stefanielinear/ai4ee-pcb/ECG12_Portable/output/3d/pcb_3d_back.png

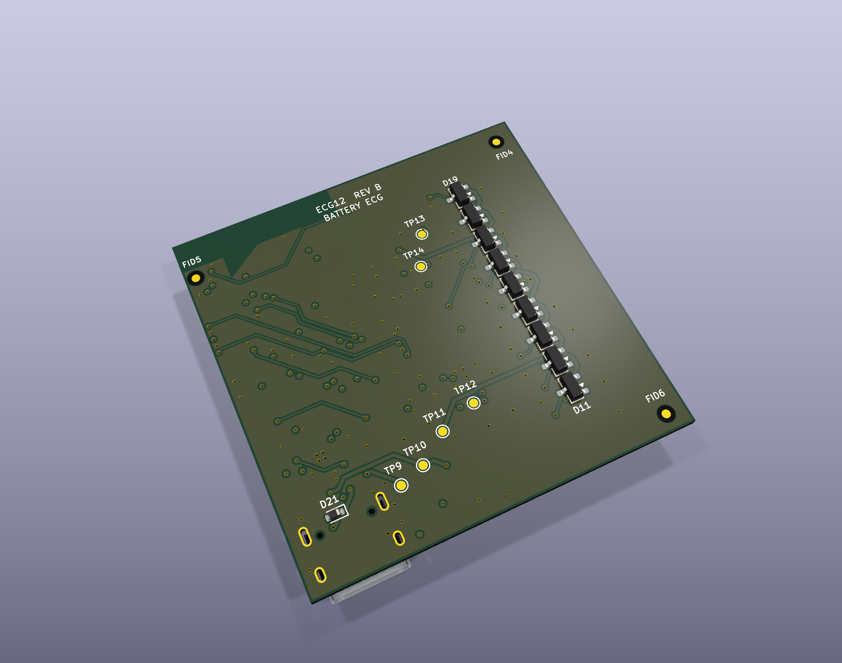
ECG12_Portable/output/3d/pcb_3d_back.png
