stefanielinear/ai4ee-pcb/ECG12_Portable/output/3d/pcb_3d_front.png

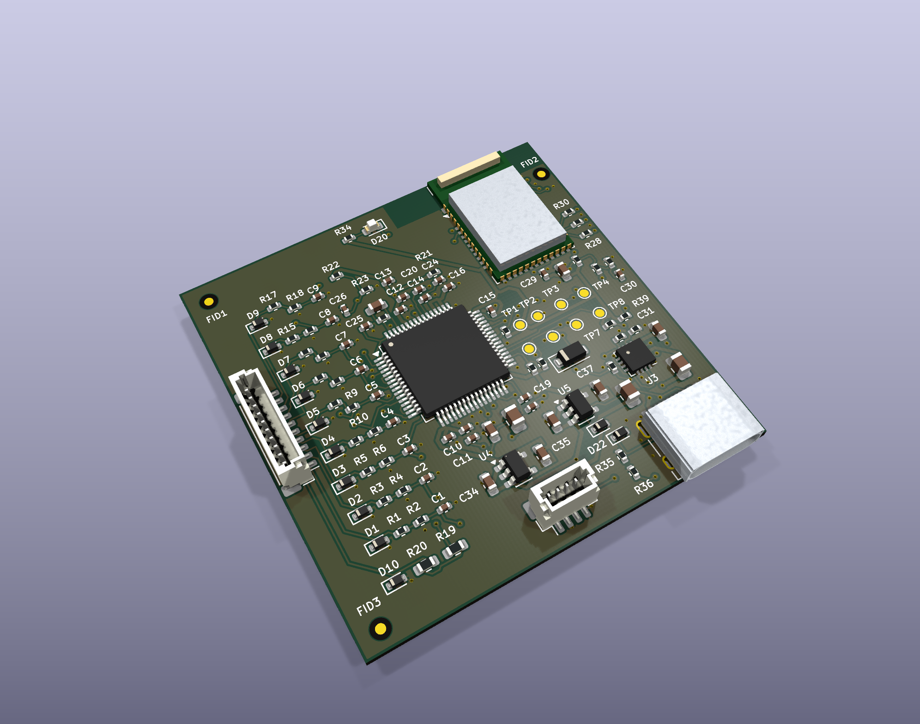
ECG12_Portable/output/3d/pcb_3d_front.png
