stefanielinear/ai4ee-pcb/ECG12_Portable/output/layers/pdf/11_F_Fab.pdf

BAT+ G NTC G | USB CHARGE
C32C32 R26R26 | R39R39 C15C15 C21C21 R12R12 | R33R33 C25C25 | R41R41 R5R5 R15R15 | TP5 TP5
C1C1 | U2 U2

D8 D8

D5 D5

J2J2 R16R16 | R21R21 C10C10 C7C7 | C27 C27 | D22 D22

D6 D6

R3R3 D1 D1

U3U R10R10 | TP1 TP1

R31R31

## FID3 FIDUCIAL

FID3 | R40R40 | R29R29 C11C11 | C35C35 R7R7 | R28R28 FID1 FIDUCIAL
FID1 | TP6 TP6

TP3 TP3

R14R14 R4R4 R6R6 | C4C4 | C33C33 R9R9 | J3J R24R24 C26C26 | C31C31 FID2 FIDUCIAL
FID2 R22R22 | C12C12 C3C3 D10 D10

C29C29 D4 D4

C8C8 | TP8 TP8
R1R1 | C22C22 R11R11 | C18C18 C6C6 | TP2 TP2
C23C23 | C19C19 J1J1
R23R23 R18R18 | C36C36 R27R27 C16C16 | U5U5
R35R35 | R32R32 D3 D3
R36R36 C9C9 | U1U1 | D23 D23 C34C34 R13R13 | D20 D20 C5C5 | R38R38 R37R37 | C28C28 D7 D7
R20 R20 | C14C14 C13C13 | R25R25 R8R8 | TP4 TP4
U4U4 C20C20 R34R34 R17R17 | C17C17 C2C2 R2R2 | C30C30 R19 R19 | D24 D24

R30R30 D2 D2

D9 D9

C24C24 | TP7 TP7

C37C37
