stefanielinear/ai4ee-pcb/ECG12_Portable/output/3d/module_dimensions.png

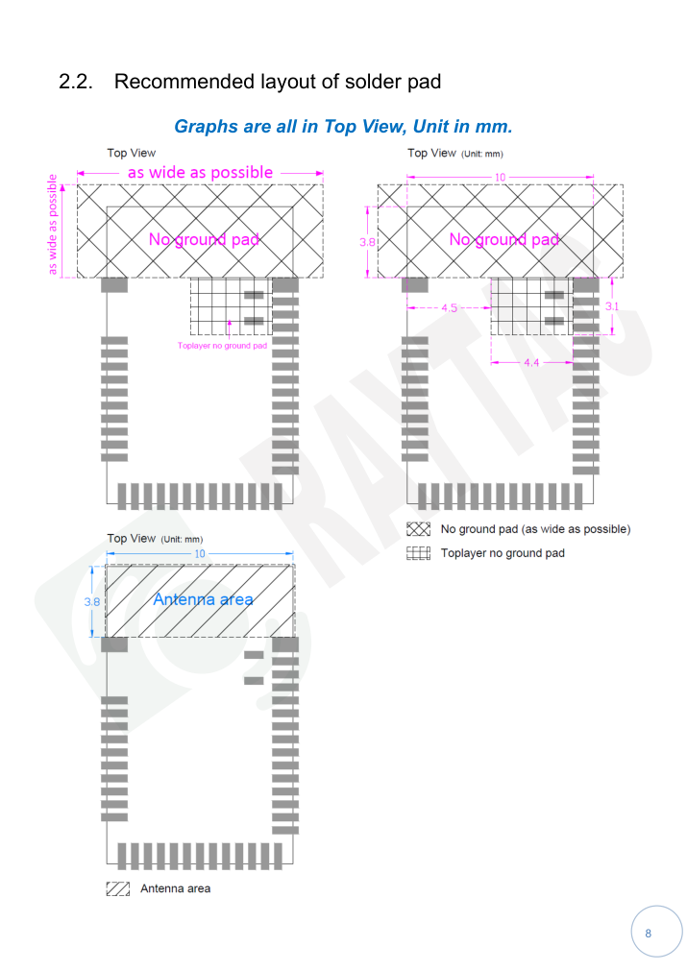
ECG12_Portable/output/3d/module_dimensions.png
