stefanielinear/ai4ee-pcb/ECG12_Portable/output/layers/01_F_Cu.png

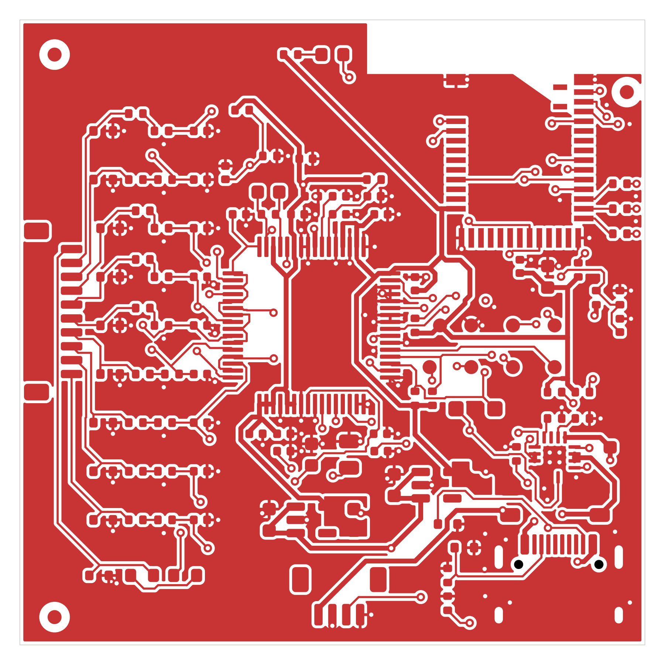
ECG12_Portable/output/layers/01_F_Cu.png
