stefanielinear/ai4ee-pcb/ECG12_Portable/output/layers/02_In1_Cu.png

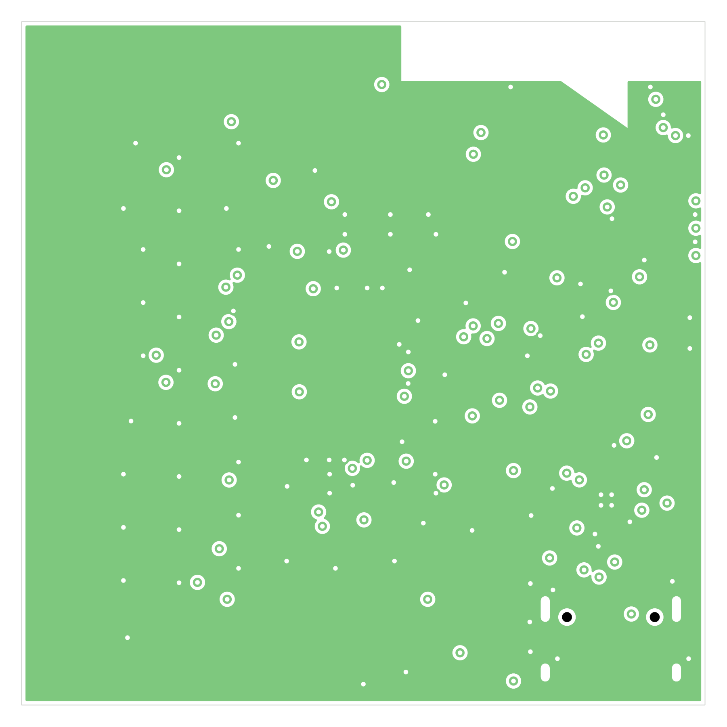
ECG12_Portable/output/layers/02_In1_Cu.png
