stefanielinear/ai4ee-pcb/ECG12_Portable/output/layers/03_In2_Cu.png

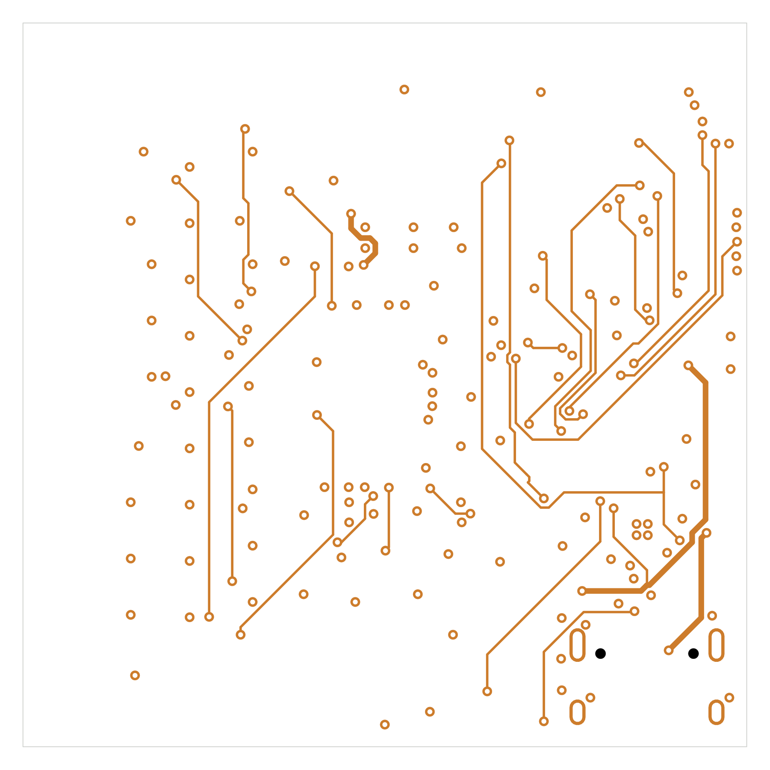
ECG12_Portable/output/layers/03_In2_Cu.png
