stefanielinear/ai4ee-pcb/ECG12_Portable/output/layers/04_B_Cu.png

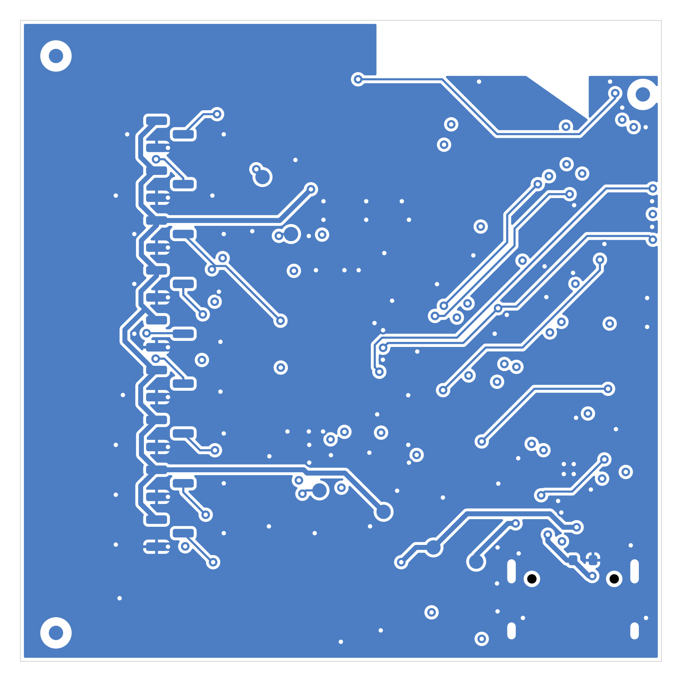
ECG12_Portable/output/layers/04_B_Cu.png
