stefanielinear/ai4ee-pcb/ECG12_Portable/output/layers/05_F_Mask.png

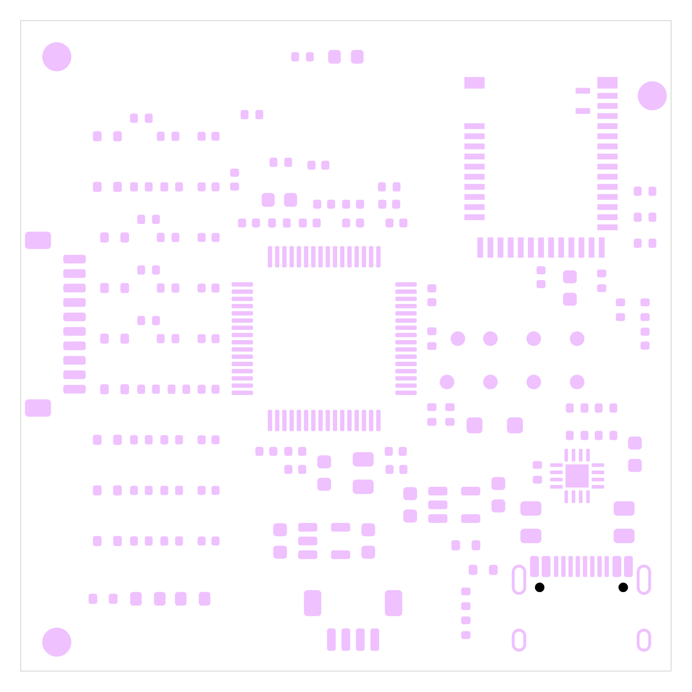
ECG12_Portable/output/layers/05_F_Mask.png
