stefanielinear/ai4ee-pcb/ECG12_Portable/output/layers/06_B_Mask.png

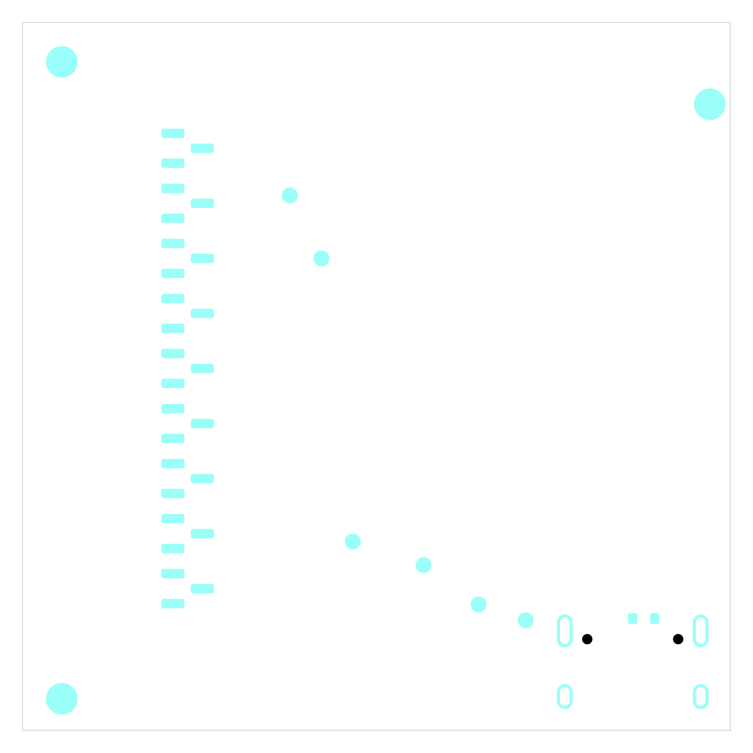
ECG12_Portable/output/layers/06_B_Mask.png
