stefanielinear/ai4ee-pcb/ECG12_Portable/output/layers/07_F_Paste.png

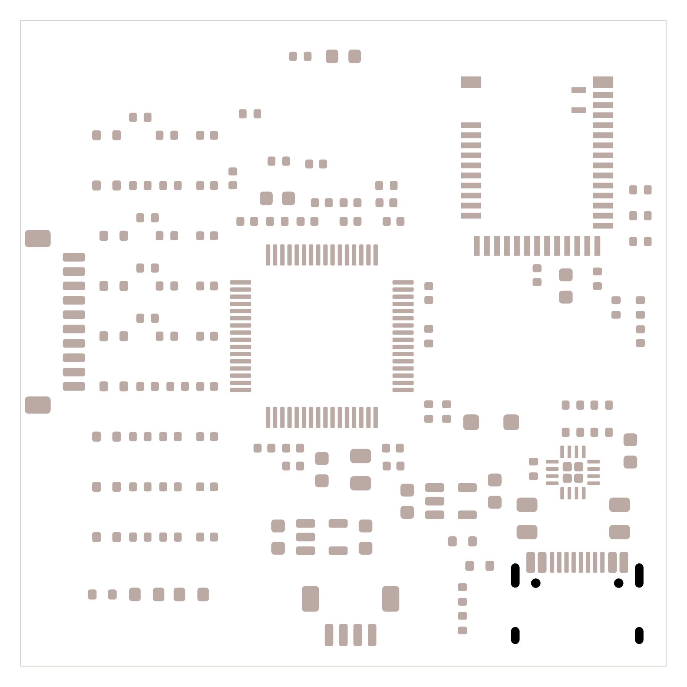
ECG12_Portable/output/layers/07_F_Paste.png
