stefanielinear/ai4ee-pcb/ECG12_Portable/output/layers/08_B_Paste.png

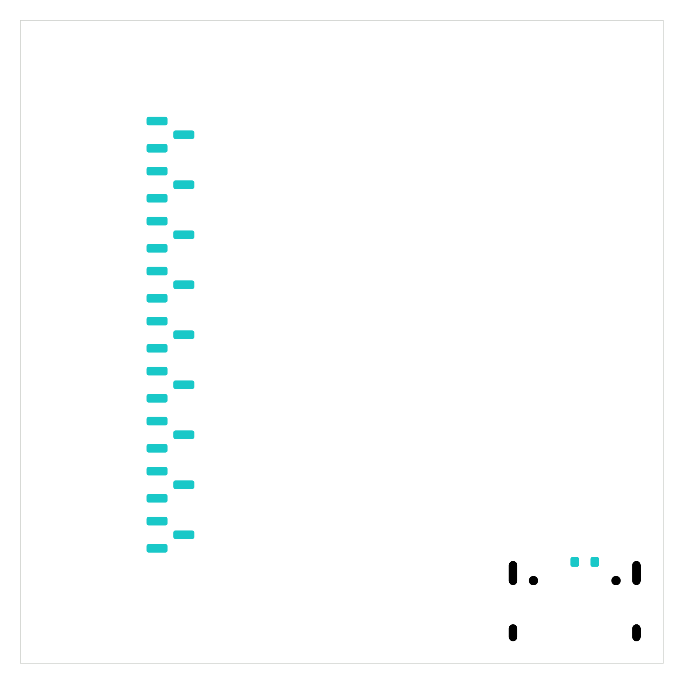
ECG12_Portable/output/layers/08_B_Paste.png
