stefanielinear/ai4ee-pcb/ECG12_Portable/output/layers/09_F_Silkscreen.png

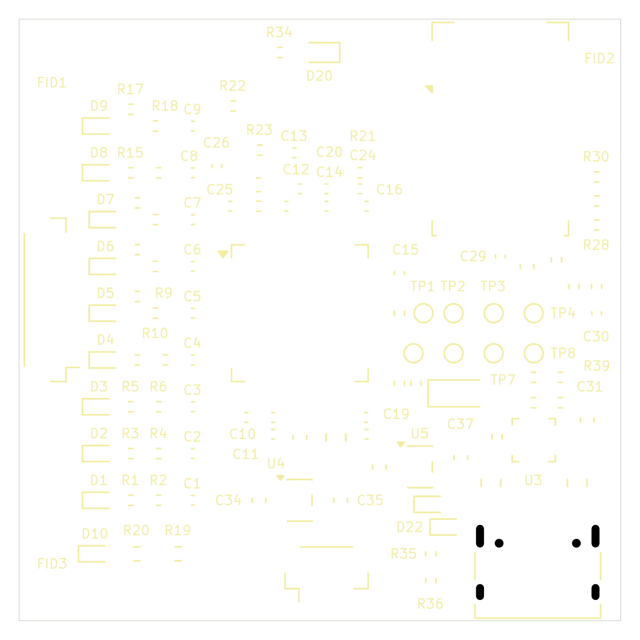
ECG12_Portable/output/layers/09_F_Silkscreen.png
