stefanielinear/ai4ee-pcb/ECG12_Portable/output/layers/10_B_Silkscreen.png

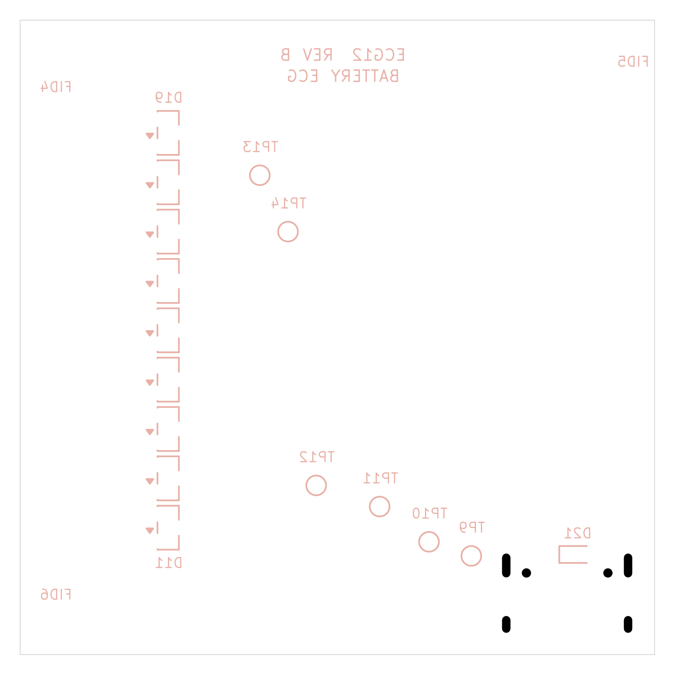
ECG12_Portable/output/layers/10_B_Silkscreen.png
