stefanielinear/ai4ee-pcb/ECG12_Portable/output/layers/11_F_Fab.png

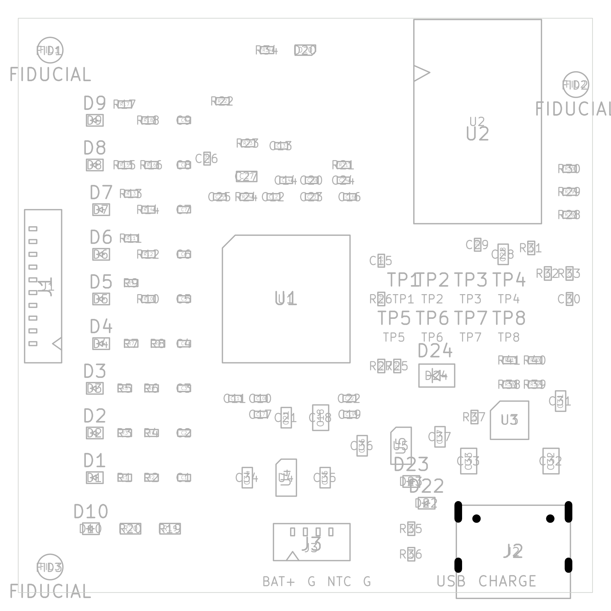
ECG12_Portable/output/layers/11_F_Fab.png
