stefanielinear/ai4ee-pcb/ECG12_Portable/output/layers/12_B_Fab.png

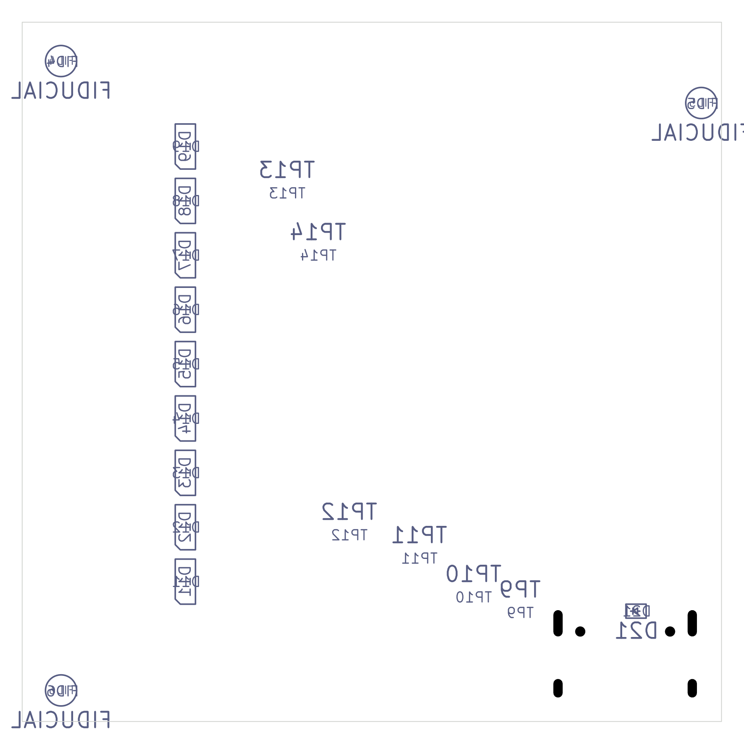
ECG12_Portable/output/layers/12_B_Fab.png
