stefanielinear/ai4ee-pcb/ECG12_Portable/output/layers/13_F_Courtyard.png

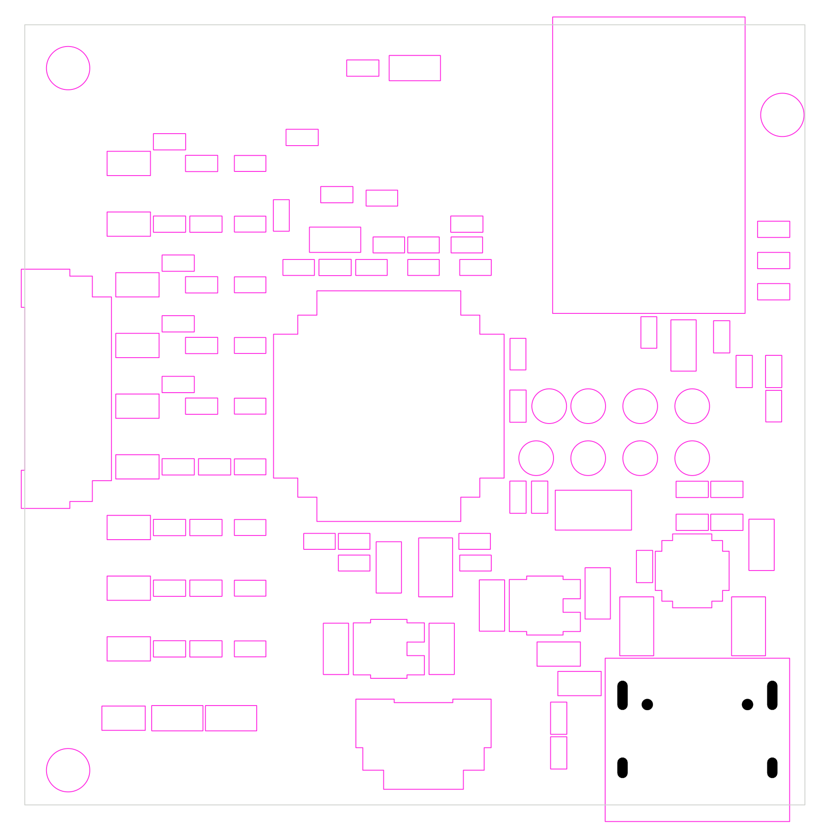
ECG12_Portable/output/layers/13_F_Courtyard.png
