stefanielinear/ai4ee-pcb/ECG12_Portable/output/layers/15_Edge_Cuts.png

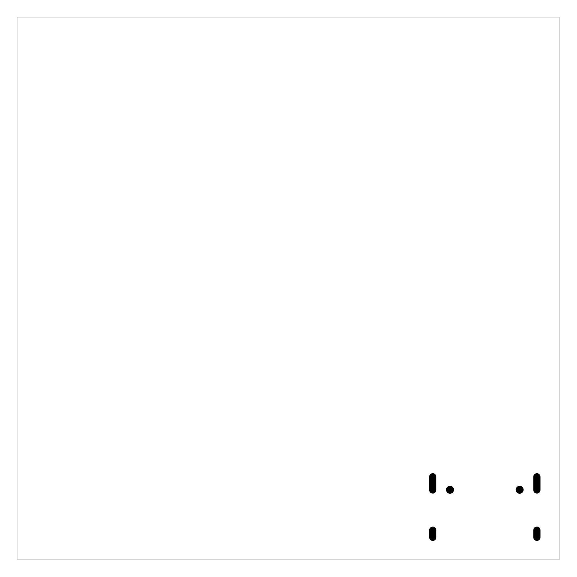
ECG12_Portable/output/layers/15_Edge_Cuts.png
