stefanielinear/ai4ee-pcb/ECG12_Portable/output/layers/copper_layers_overview.png

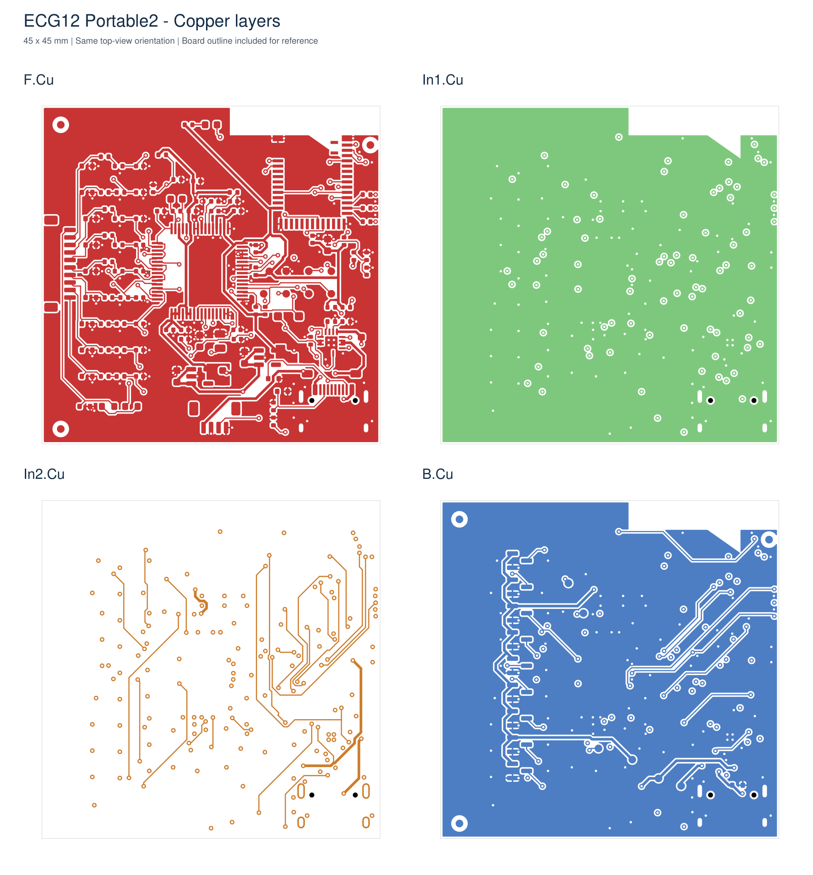
ECG12_Portable/output/layers/copper_layers_overview.png
