stefanielinear/ai4ee-pcb/ECG12_Portable/output/schematic_images/01_System.png

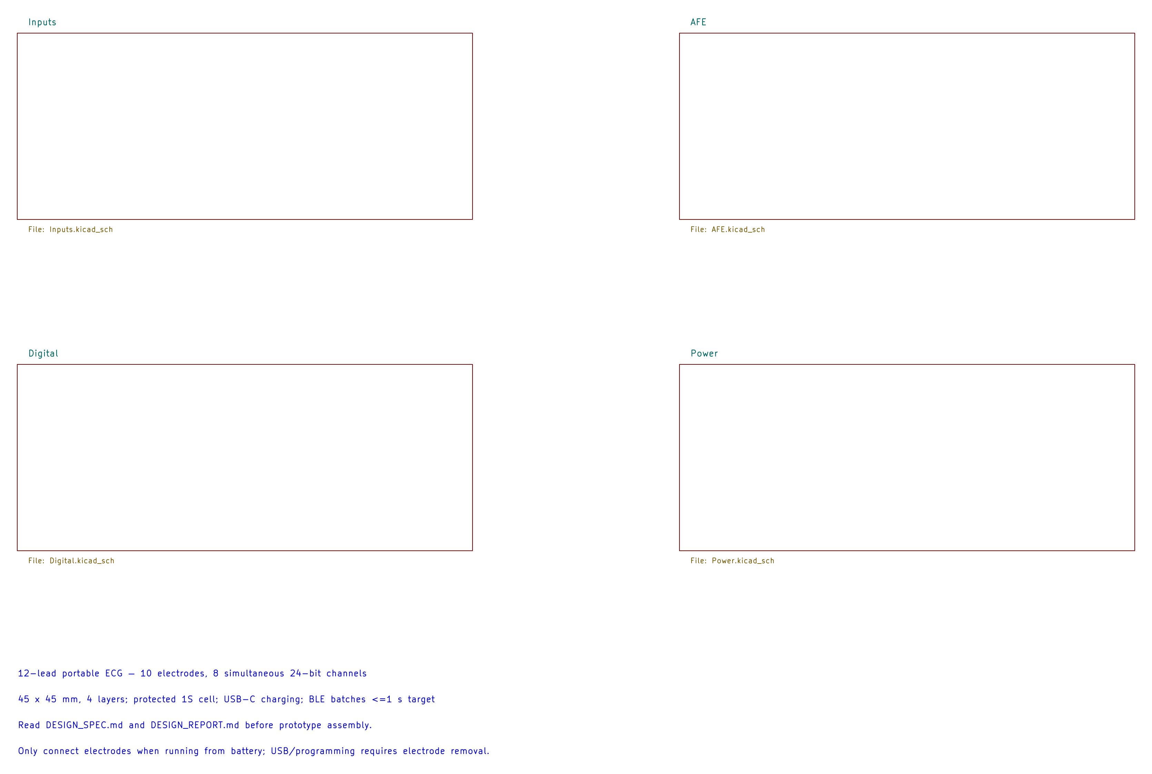
ECG12_Portable/output/schematic_images/01_System.png
