stefanielinear/ai4ee-pcb/ECG12_Portable/output/schematic_images/02_Inputs.png

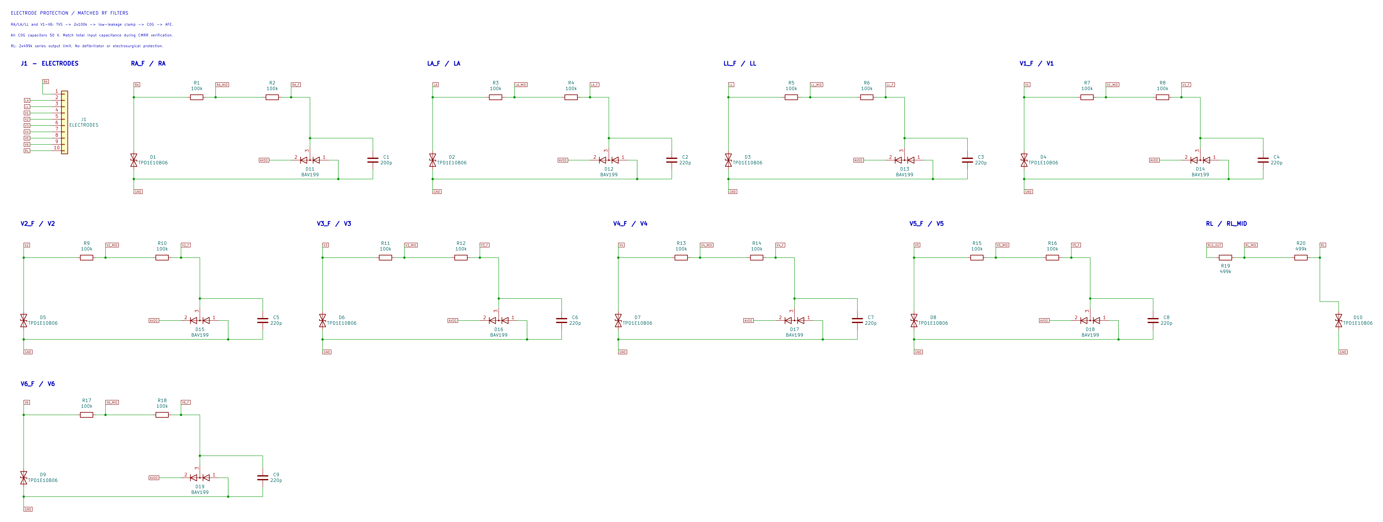
ECG12_Portable/output/schematic_images/02_Inputs.png
