stefanielinear/ai4ee-pcb/ECG12_Portable/output/schematic_images/03_AFE.png

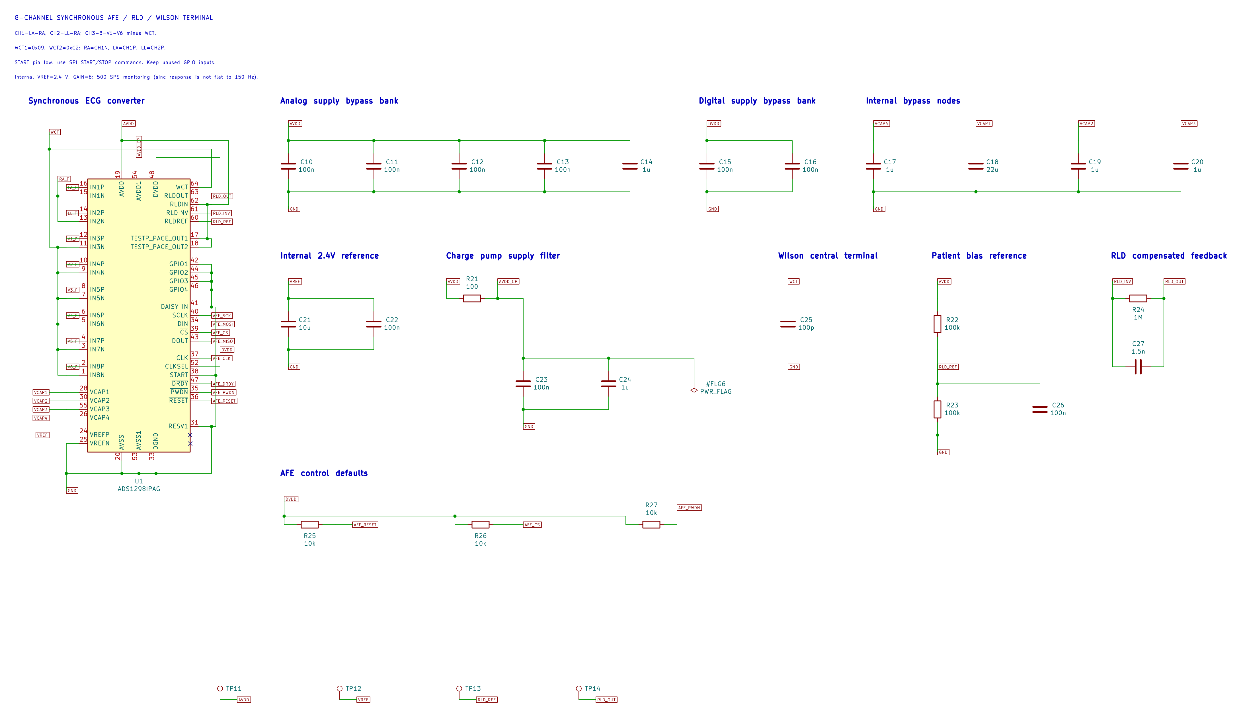
ECG12_Portable/output/schematic_images/03_AFE.png
