stefanielinear/ai4ee-pcb/ECG12_Portable/output/schematic_images/04_Digital.png

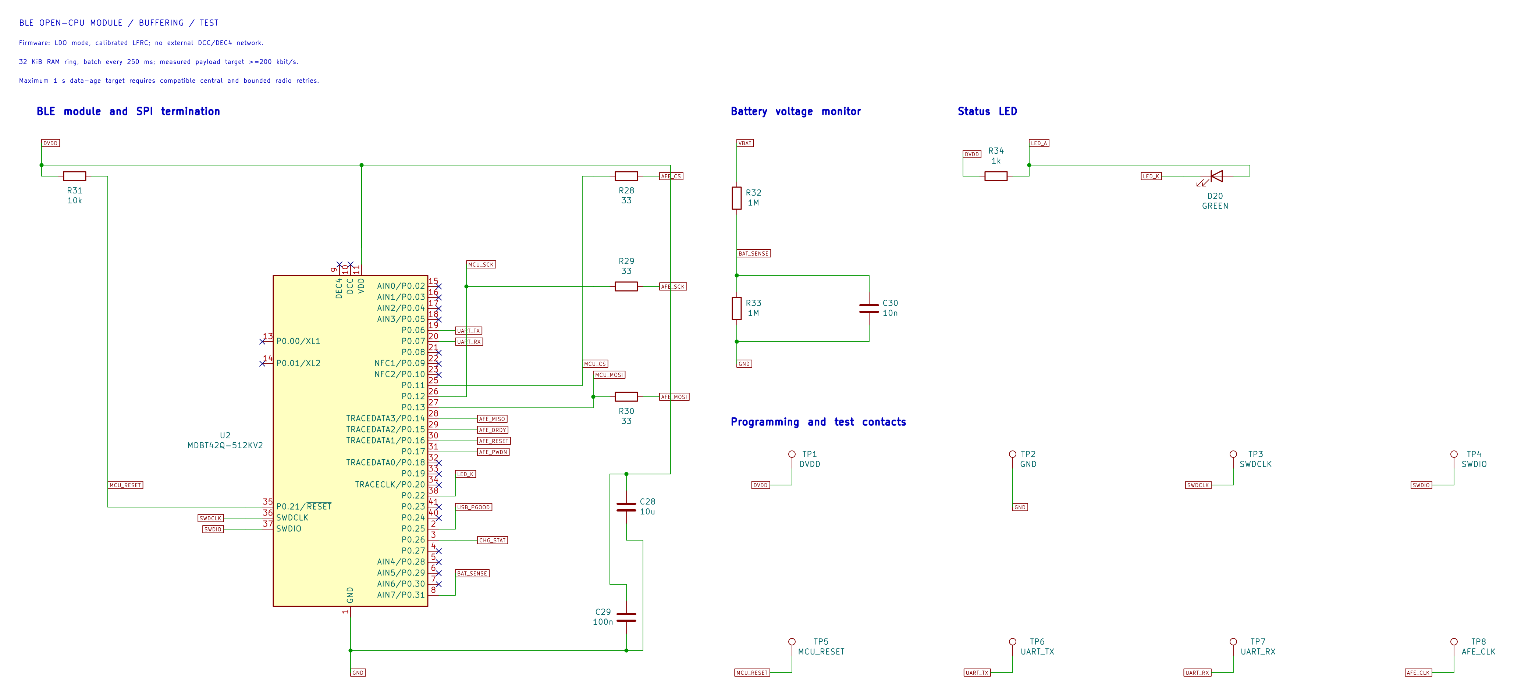
ECG12_Portable/output/schematic_images/04_Digital.png
