stefanielinear/ai4ee-pcb/ECG12_Portable/output/schematic_images/full_pages/01_System.png

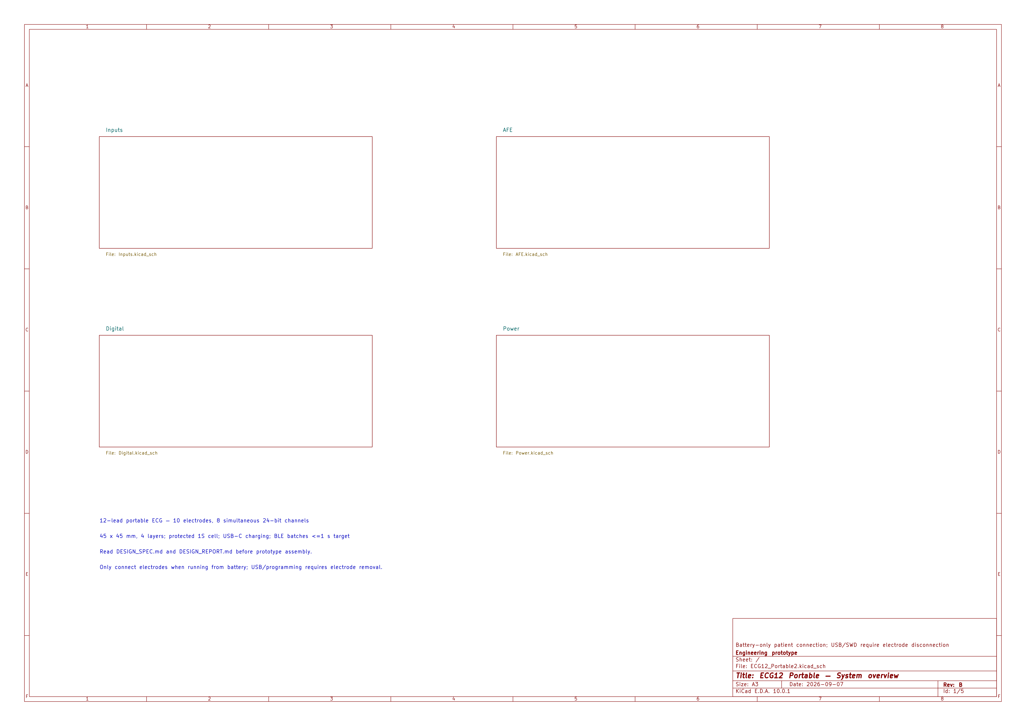
ECG12_Portable/output/schematic_images/full_pages/01_System.png
