stefanielinear/ai4ee-pcb/ECG12_Portable/output/schematic_images/full_pages/04_Digital.png

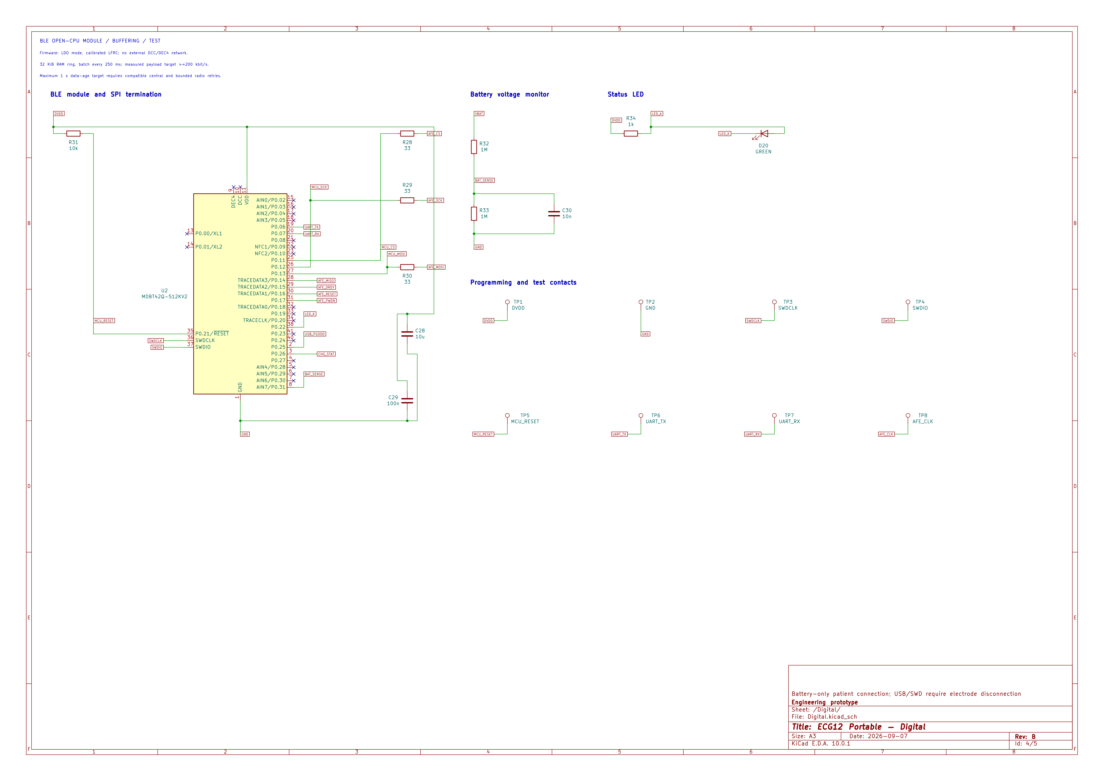
ECG12_Portable/output/schematic_images/full_pages/04_Digital.png
