stefanielinear/ai4ee-pcb/ECG12_Portable/output/schematic_images/full_pages/05_Power.png

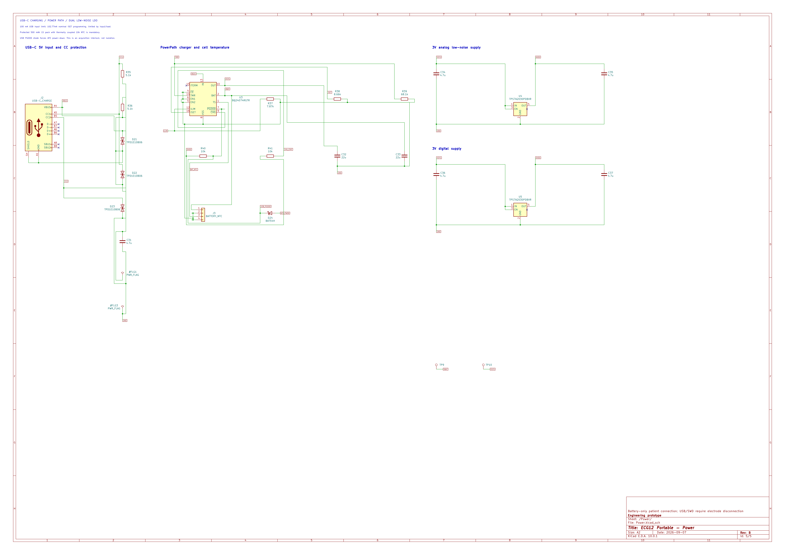
ECG12_Portable/output/schematic_images/full_pages/05_Power.png
