stefanielinear/ai4ee-pcb/ECG12_Portable/output/schematic_images/overview.png

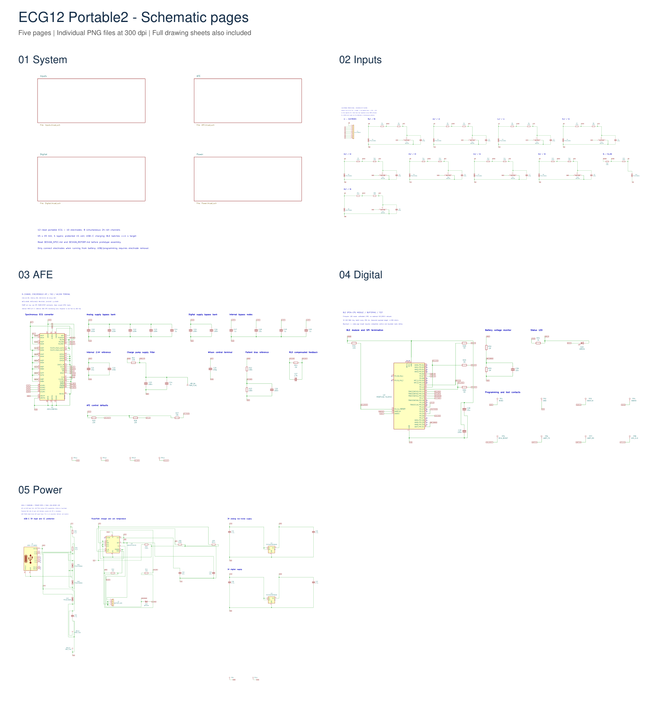
ECG12_Portable/output/schematic_images/overview.png
