stefanielinear/ai4ee-pcb/ECG12_Portable/production/drawings/ground_plane.pdf

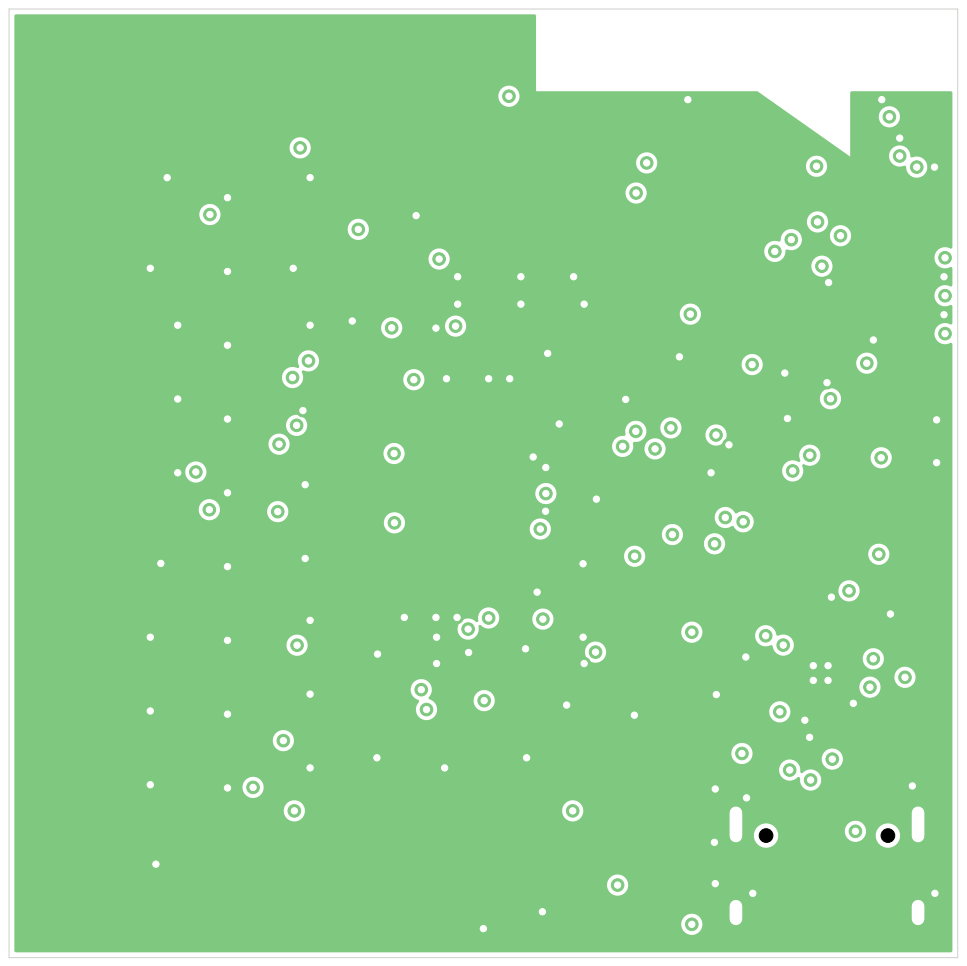
[picture p69: page 1]
