stefanielinear/ai4ee-pcb/ECG12_Portable/output/layers/pdf/01_F_Cu.pdf

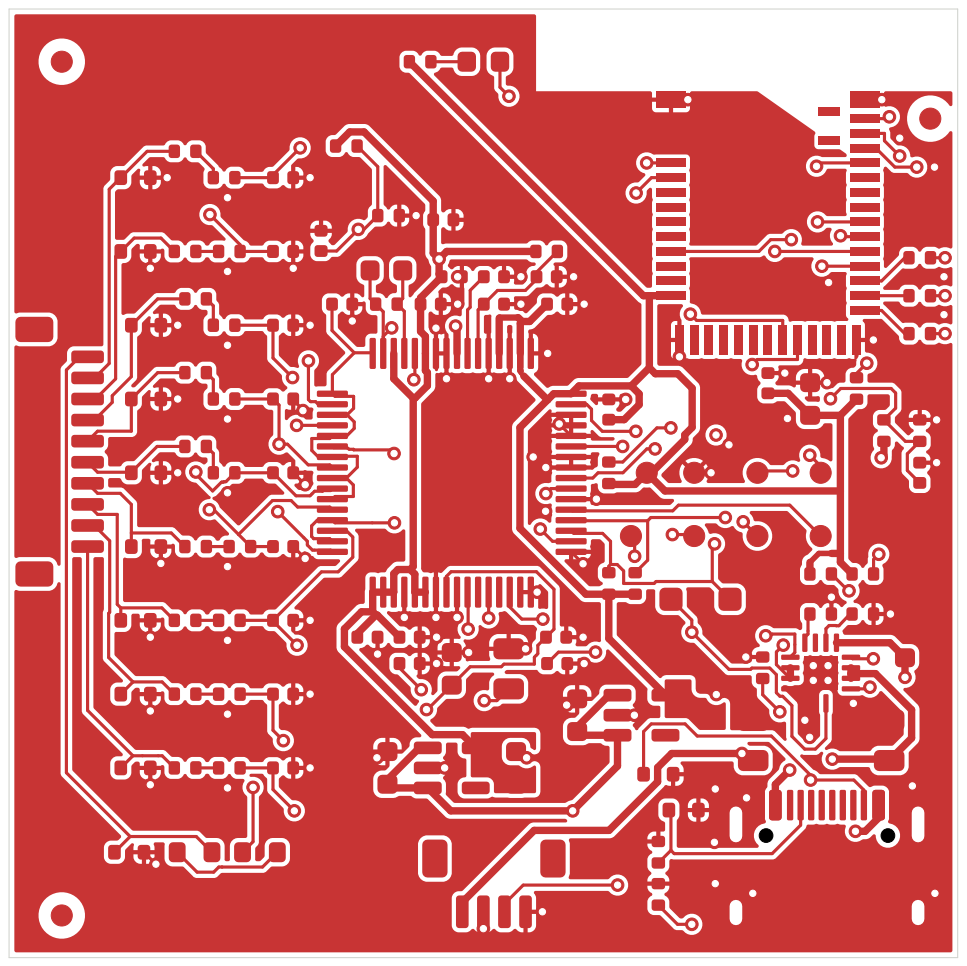
[picture p70: page 1]
