stefanielinear/ai4ee-pcb/ECG12_Portable/output/layers/pdf/03_In2_Cu.pdf

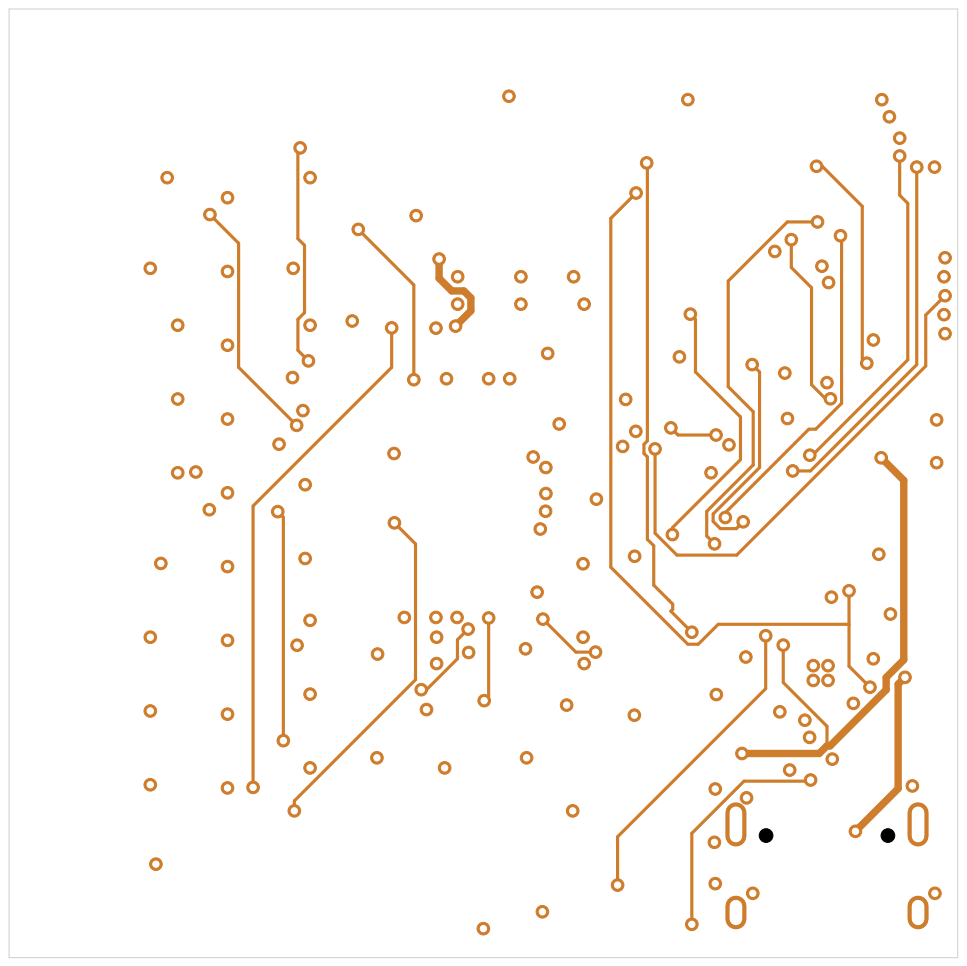
[picture p71: page 1]
