stefanielinear/ai4ee-pcb/ECG12_Portable/output/layers/pdf/04_B_Cu.pdf

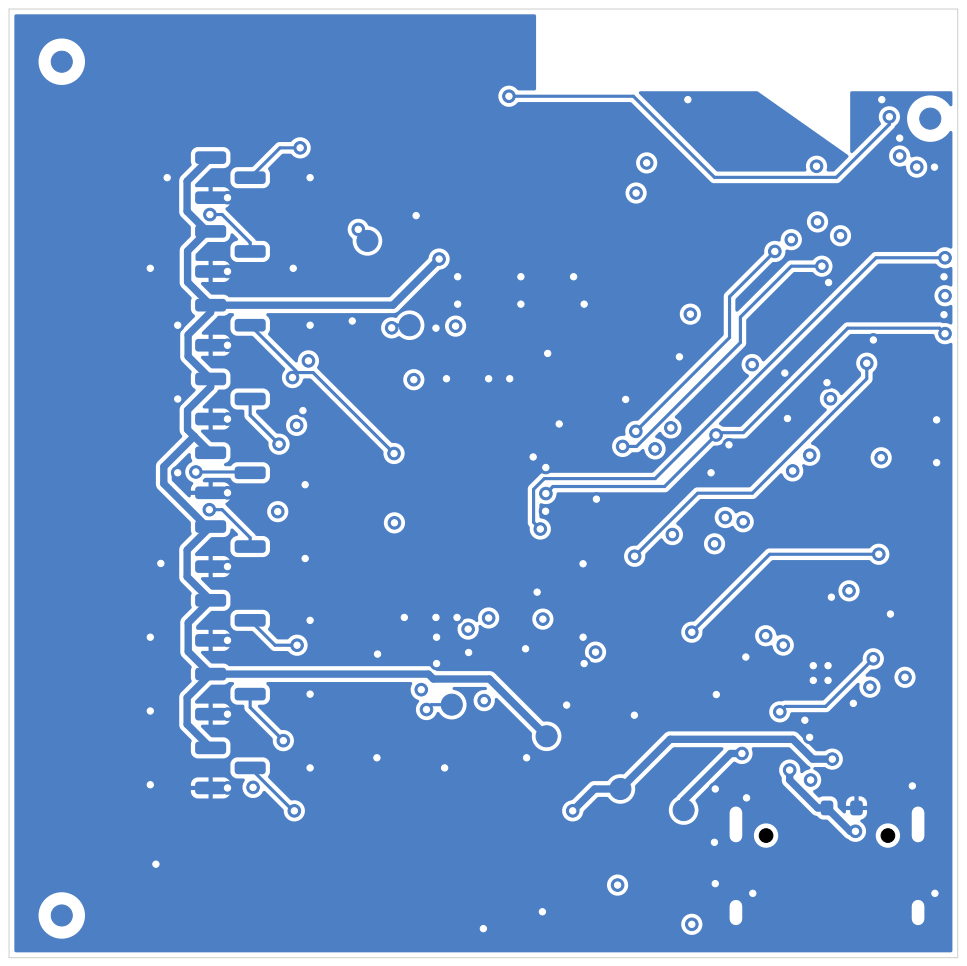
[picture p72: page 1]
