stefanielinear/ai4ee-pcb/ECG12_Portable/output/layers/pdf/05_F_Mask.pdf

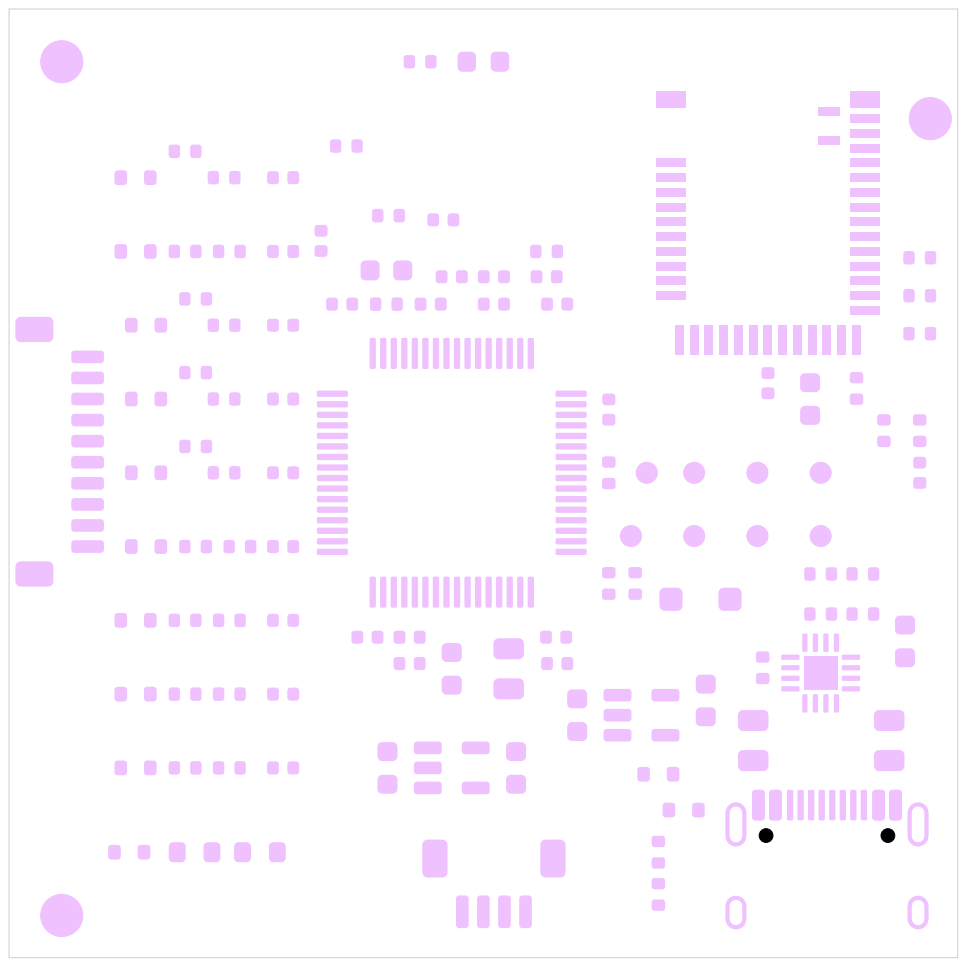
[picture p73: page 1]
