stefanielinear/ai4ee-pcb/ECG12_Portable/output/layers/pdf/06_B_Mask.pdf

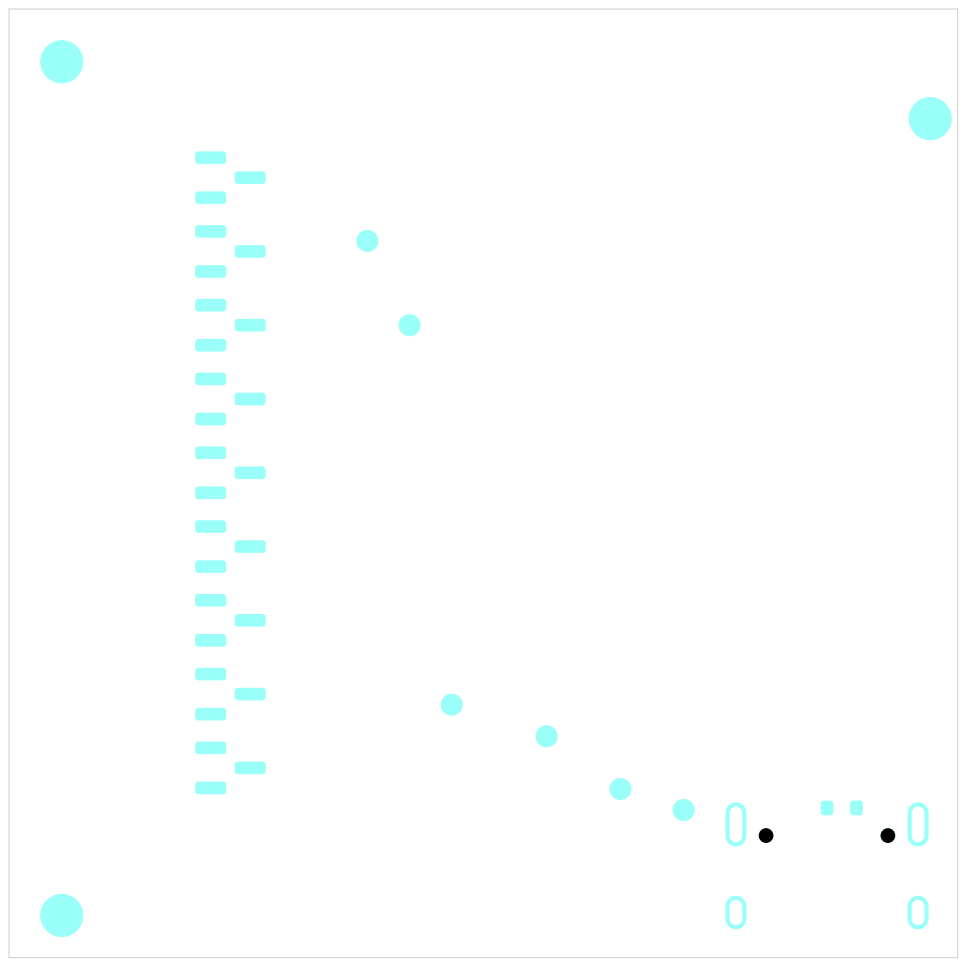
[picture p74: page 1]
