stefanielinear/ai4ee-pcb/ECG12_Portable/output/layers/pdf/07_F_Paste.pdf

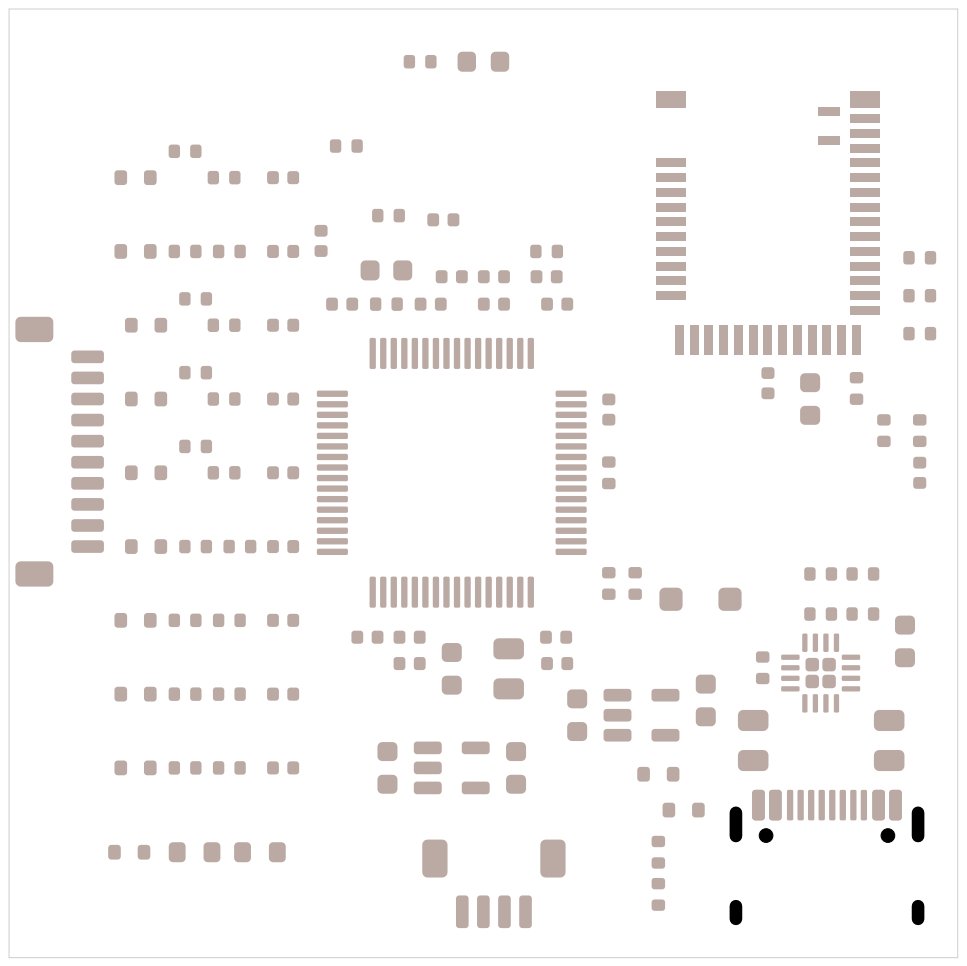
[picture p75: page 1]
