stefanielinear/ai4ee-pcb/ECG12_Portable/output/layers/pdf/08_B_Paste.pdf

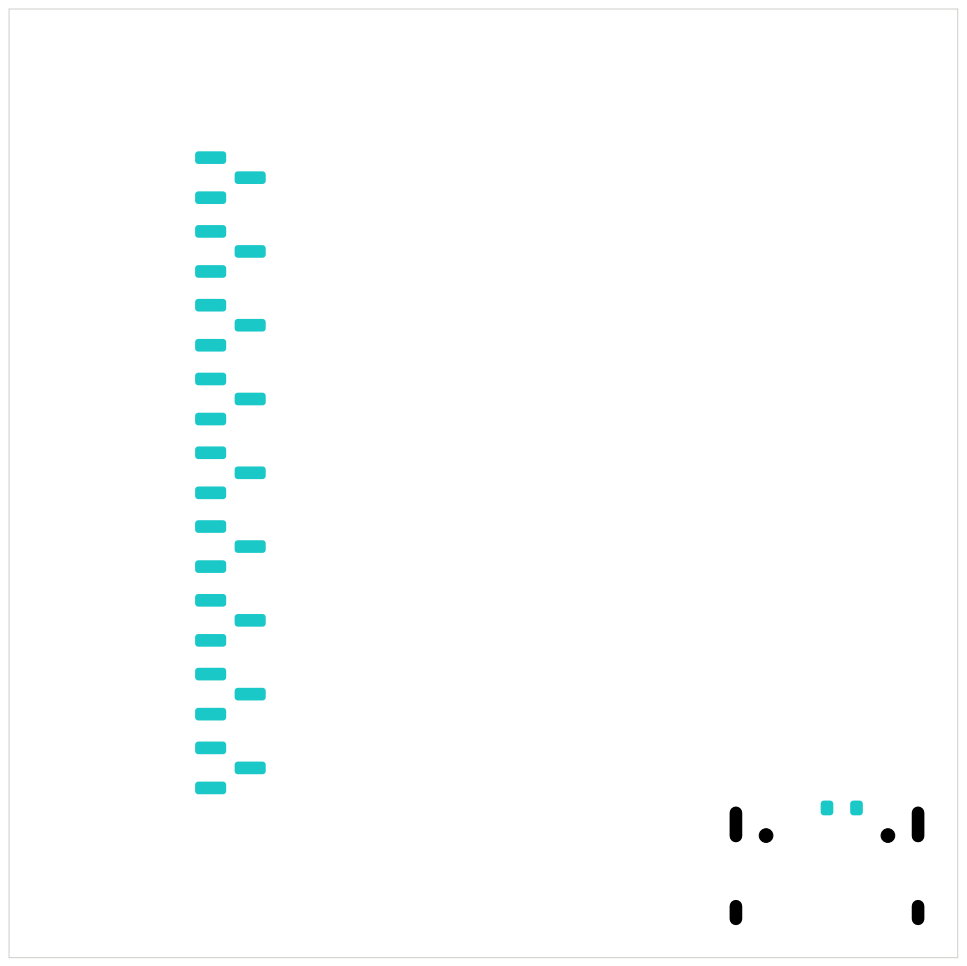
[picture p76: page 1]
