stefanielinear/ai4ee-pcb/ECG12_Portable/output/layers/pdf/09_F_Silkscreen.pdf

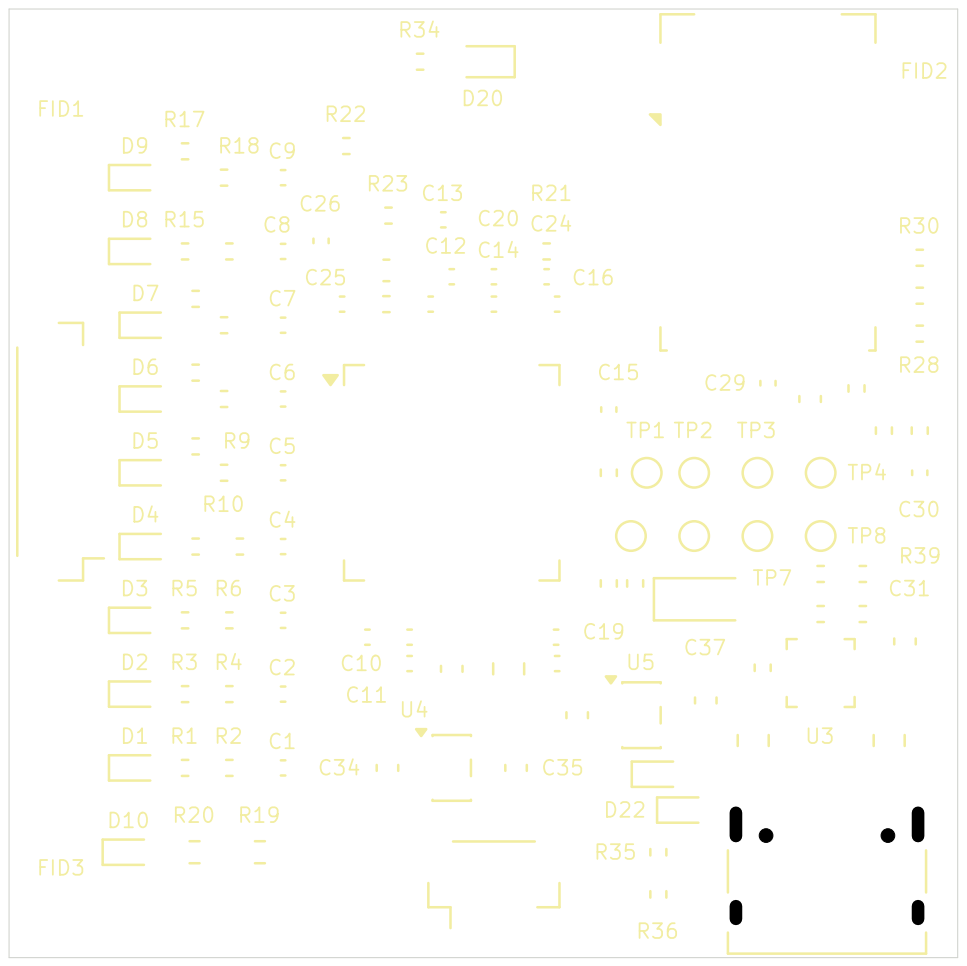
[picture p77: page 1]
