stefanielinear/ai4ee-pcb/ECG12_Portable/output/layers/pdf/10_B_Silkscreen.pdf

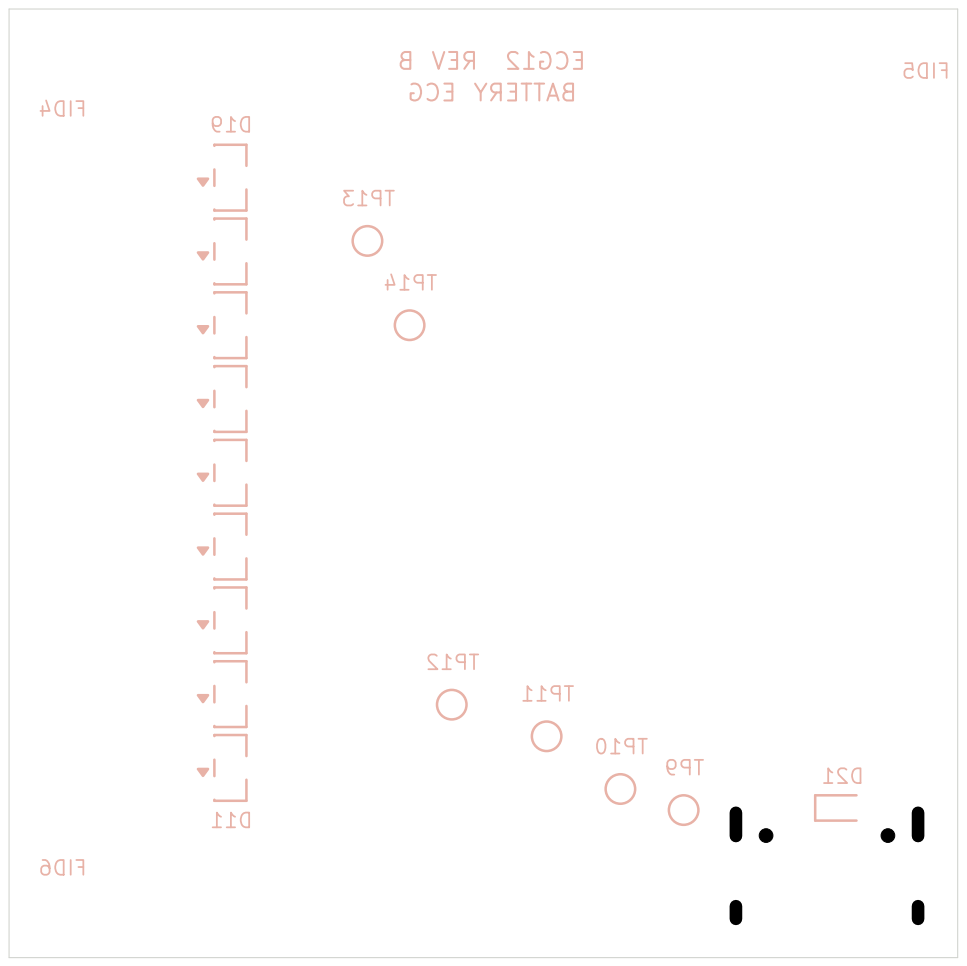
[picture p78: page 1]
