stefanielinear/ai4ee-pcb/ECG12_Portable/output/layers/pdf/12_B_Fab.pdf

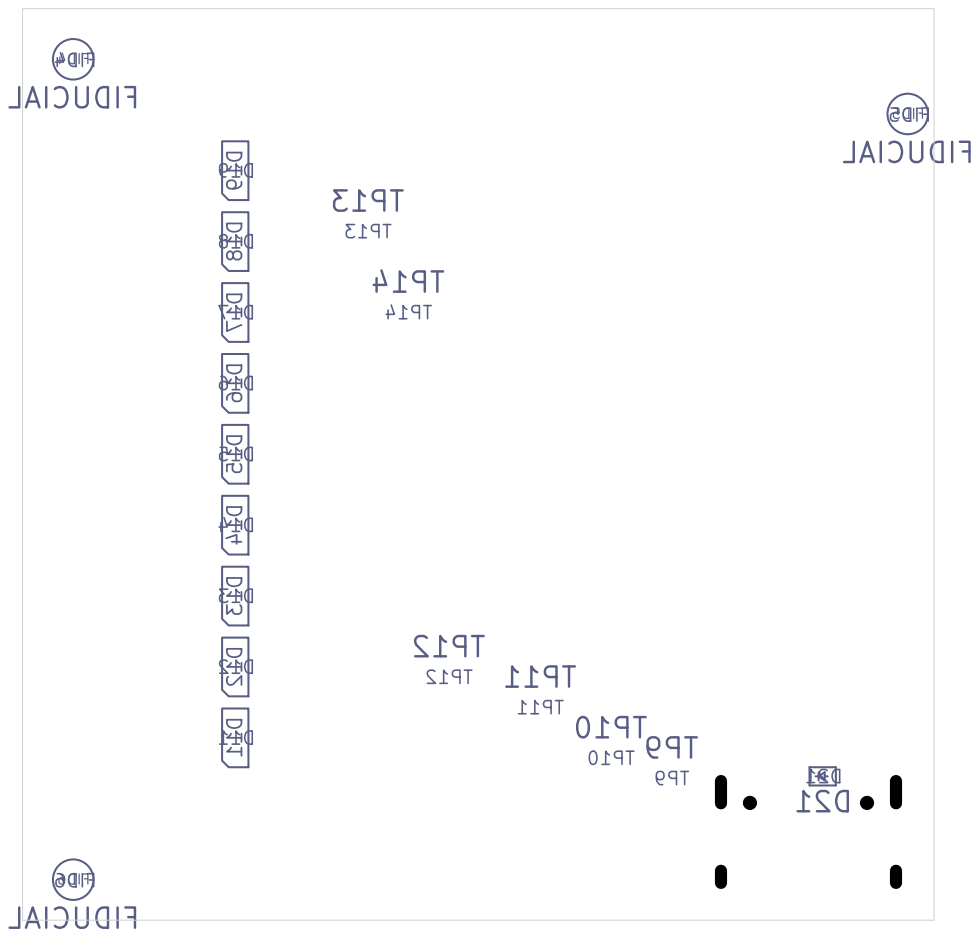
[picture p79: page 1]
