stefanielinear/ai4ee-pcb/ECG12_Portable/output/layers/pdf/13_F_Courtyard.pdf

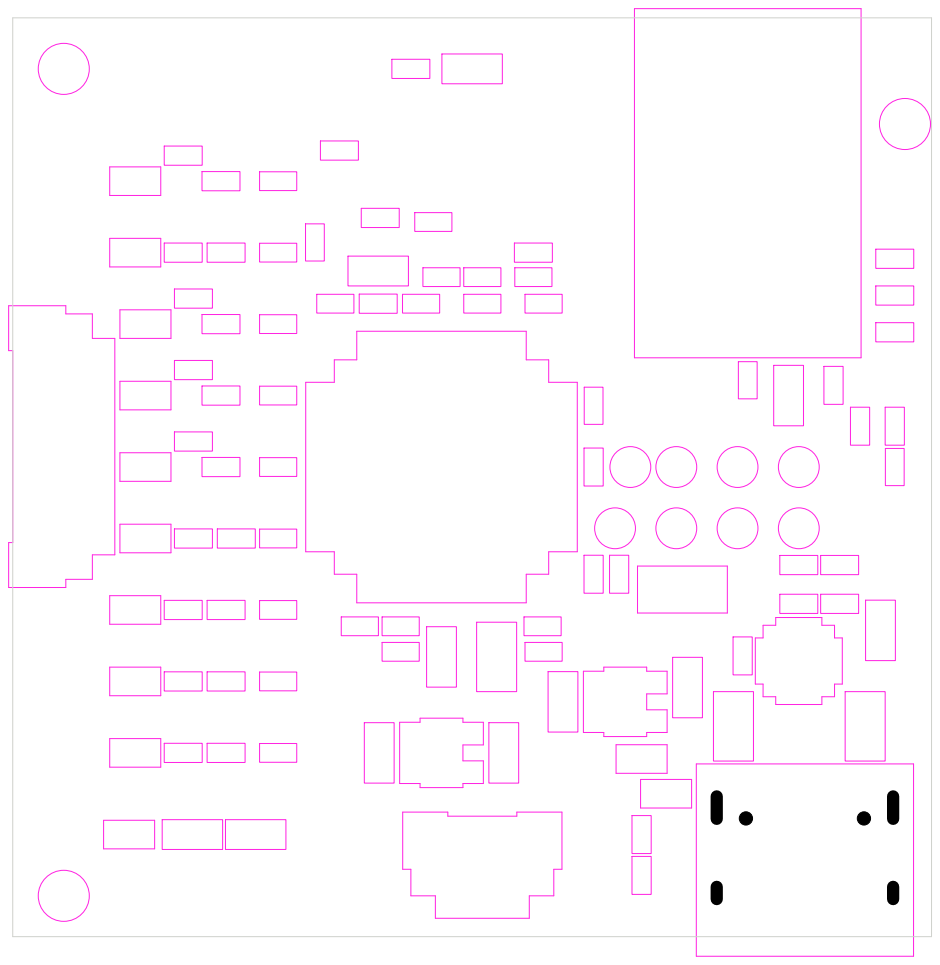
[picture p80: page 1]
