stefanielinear/ai4ee-pcb/ECG12_Portable/output/layers/pdf/14_B_Courtyard.pdf

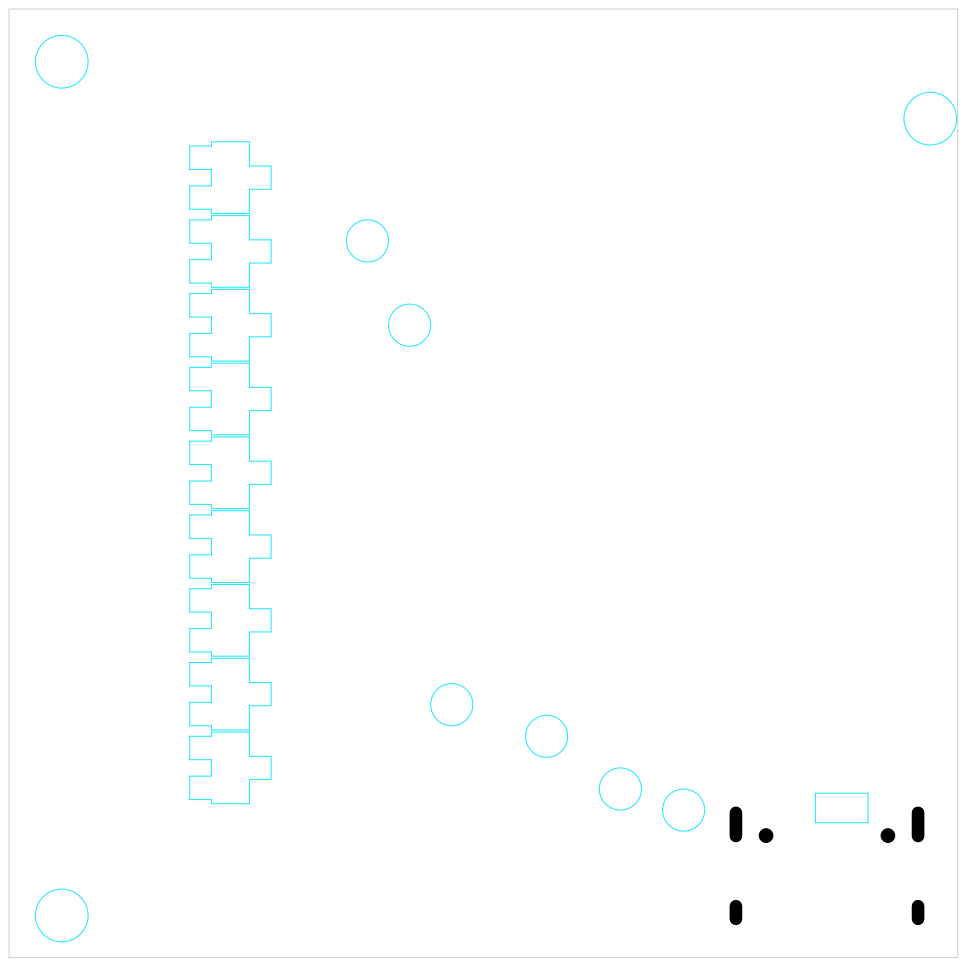
[picture p81: page 1]
