stefanielinear/ai4ee-pcb/ECG12_Portable/output/layers/pdf/15_Edge_Cuts.pdf

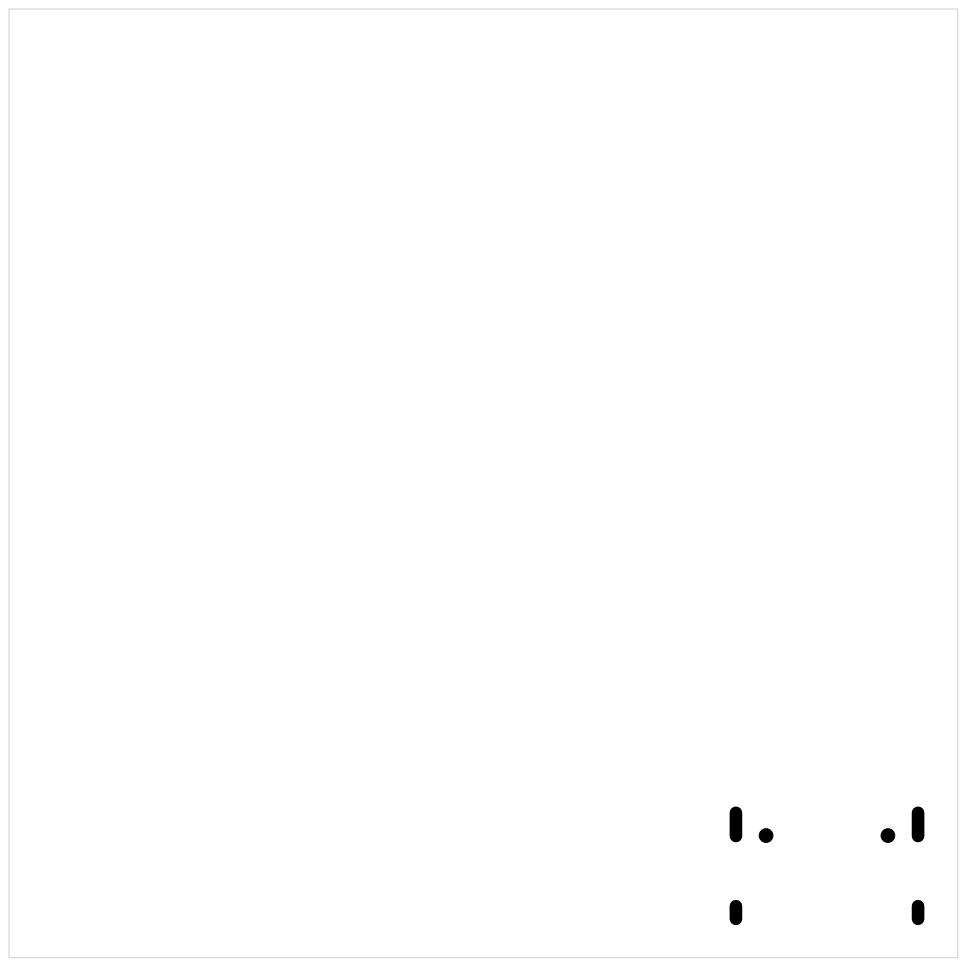
[picture p82: page 1]
