stefanielinear/ai4ee-pcb/ECG12_Portable/output/layers/pdf/18_User_Drawings.pdf

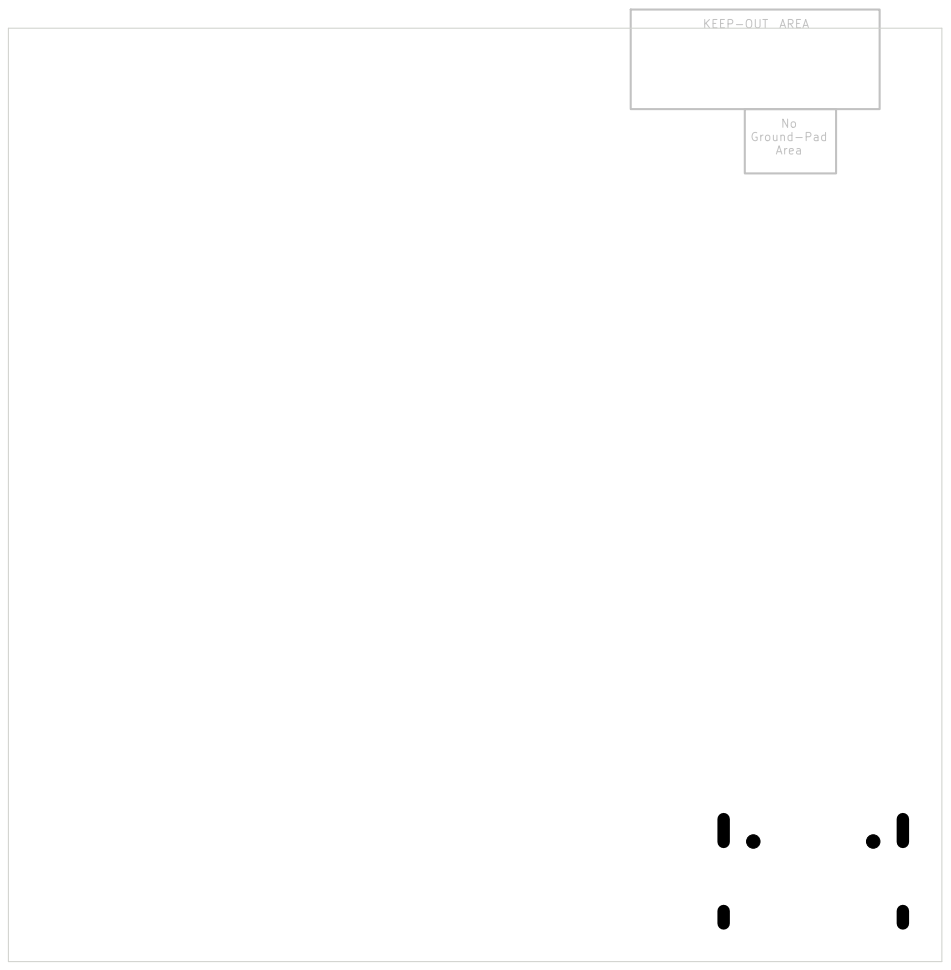
[picture p83: page 1]

Area KEEP-OUT AREA
